Caveatron/Caveatron/RevB/documentation/RPLidar_modification_alternative_ver_02.pdf

## Lidar improvement

### Version: 2019.11.22 By Szymon Kostka

### Overview:

### Tests of the original lidar design

A. 4 mm thickness flat acrylic glass, about 20 mm distance between lidar and glass:

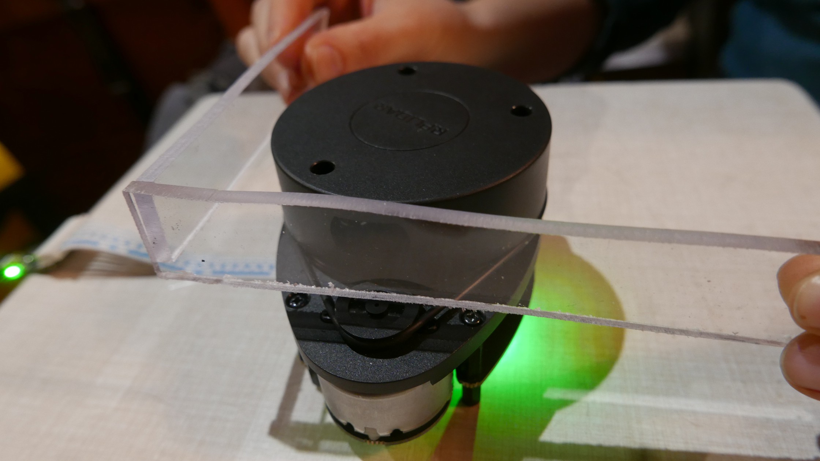
[picture p13: figure]

Test condions

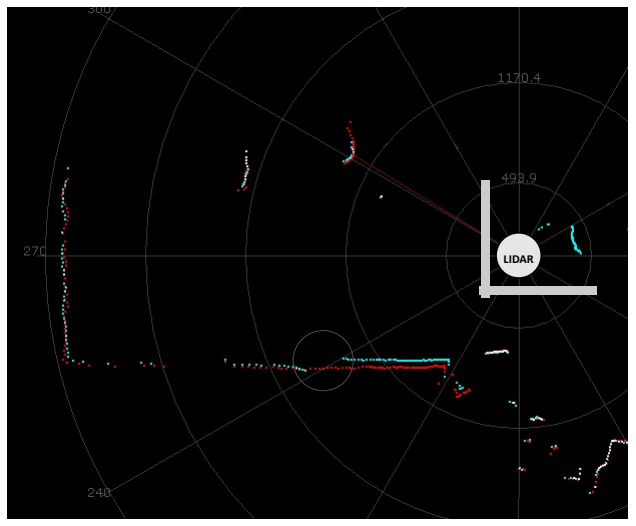
[picture p14: figure]
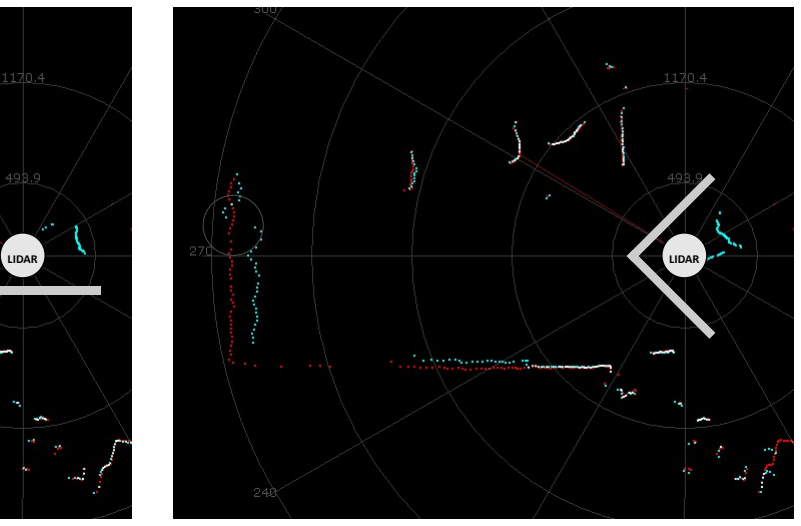
[picture p15: figure]
LIDAR

Scans. Blue dots: current state; red dots: reference image without distoron. Grey lines shows window posion.
A dark gray circle shows the locaon of the largest distorons.

Preparing to construct the housing for the lidar module, I decided to check what window shape would be the best. During the first tests, it turned out that the lidar opcal system is very sensive to distorons caused by the opcal properes of the shape and material of which the windows are made.
Tests have shown that windows made of straight secons of organic glass cause only local, but significant distorons. A window made of a pipe gives a very high distoron, the greater the farther away the scanned surface is. These distorons in the case of a pipe are also dependent on the wall thickness and distance from the opcal system. The thicker the wall and the closer to the opcs, the greater the distoron.

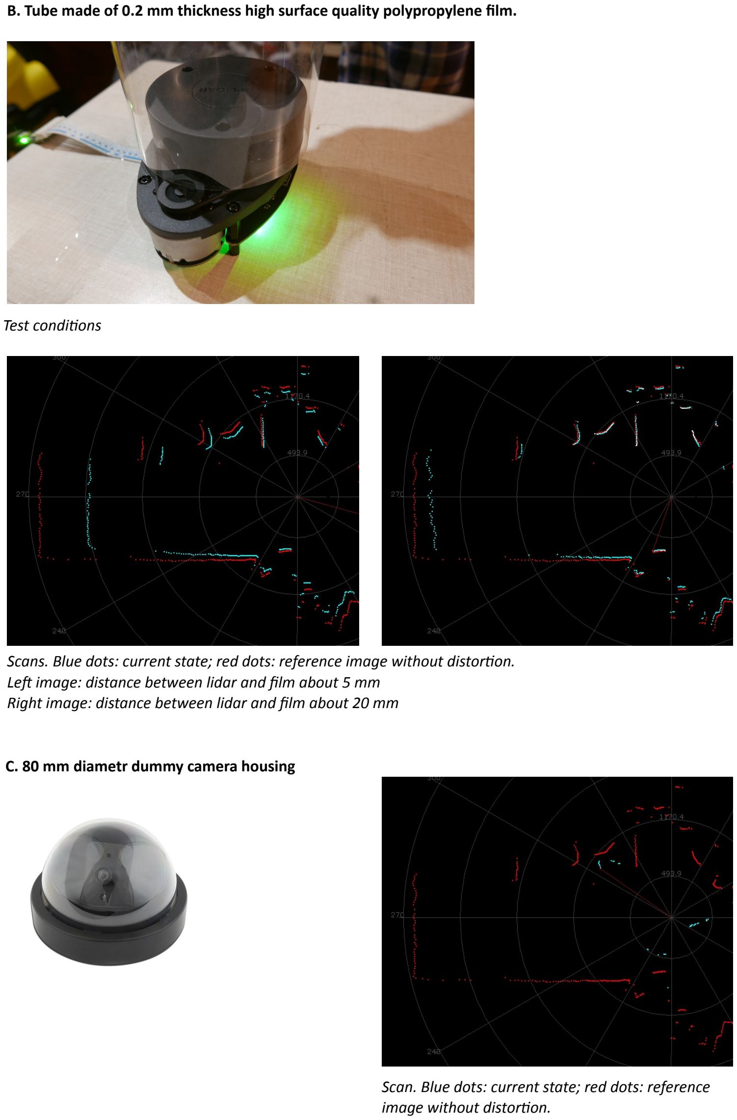
[picture p16: page 2]

B. Tube made of 0.2 mm thickness high surface quality polypropylene film.

Test condions

Scans. Blue dots: current state; red dots: reference image without distoron. Le image: distance between lidar and film about 5 mm
Right image: distance between lidar and film about 20 mm
C. 80 mm diametr dummy camera housing

Scan. Blue dots: current state; red dots: reference image without distoron.

### Conclusions:

### Modificaon of the lidar module:

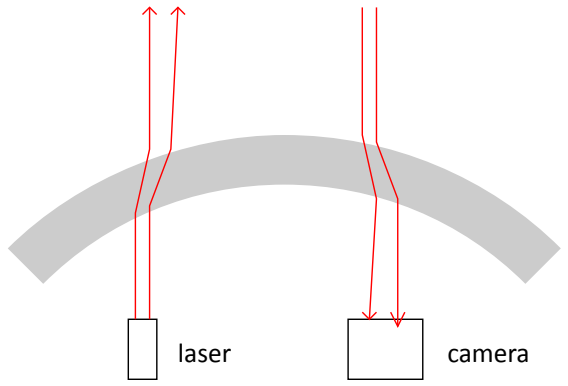
[picture p17: figure]
laser; camera

laser | camera

Simplified opcal model of different shapes of window Le: flat glass. Right: bended glass (acts as a lens).

laser
camera

Proposed modificaon of lidar, in which the laser and camera will work in the same axis.

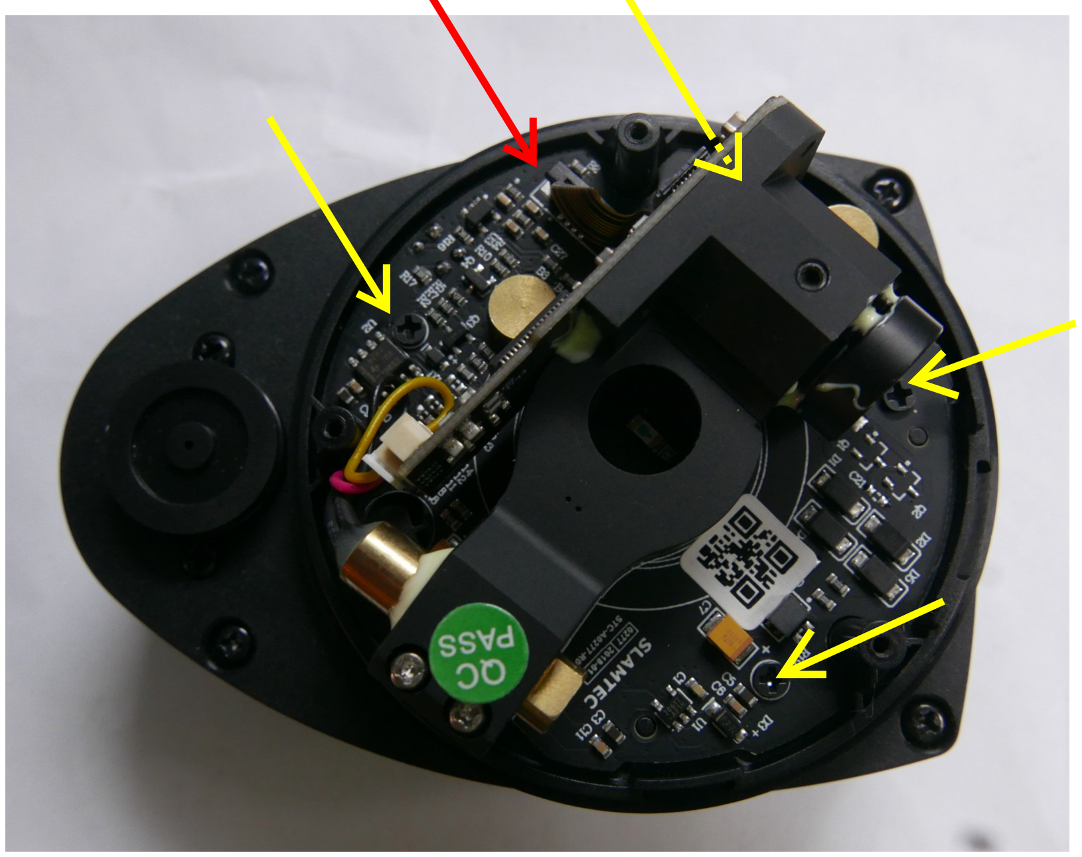
[picture p18: figure]

A.
- Remove drive belt
- Remove top cover.
- Disconnect the connecng tape from pcb pulling the brown lock out of the connector (red arrow)
- Unscrew 4 screws (yellow arrows):

The conducted experiments show that the shape of the lidar opcal path is distorted in various ways.
It mainly depends on the angle at which the lidar opcs are set to the window material. In flat glass,
the opcal path is mainly shied. In bent glass, the lens effect, which can almost completely disturb the operaon of lidar, has the greatest impact. Most of these distorons are affected by the fact that the laser
and camera work at different angles to the window material. Some soluon to the problem could be reworking the lidar so that the laser and camera work in one axis. Then the laser and camera shis should be the same. The conducted experiments and problem analysis show that a window from a tube (bent glass) will work worse than from straight glass secons.

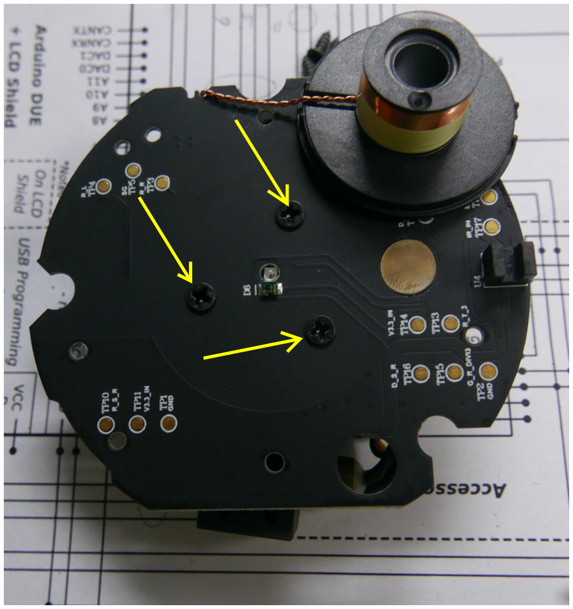
[picture p19: figure]

A.
- Remove drive belt
- Remove top cover.
- Disconnect the connecng tape from pcb pulling the brown lock out of the connector (red arrow)
- Unscrew 4 screws (yellow arrows):

C.
- Prepare a new fastening element for lidar opcs. Use an aluminum angle 2 mm thick.

47,50 mm

28,00 mm

You can draw holes with a transparent adhesive tape. You can also print an unfolded drawing, sck it on aluminum and punch the holes with a center punch

expanded drawing (1:1)

holes:
1.5 mm dia and thread M2
(metric!) for original screws
or 2 - 2.2 mm for screws with nut

holes:
Outside: 2 - 2.2 mm.

# Center: 3 mm ²²,00 mm

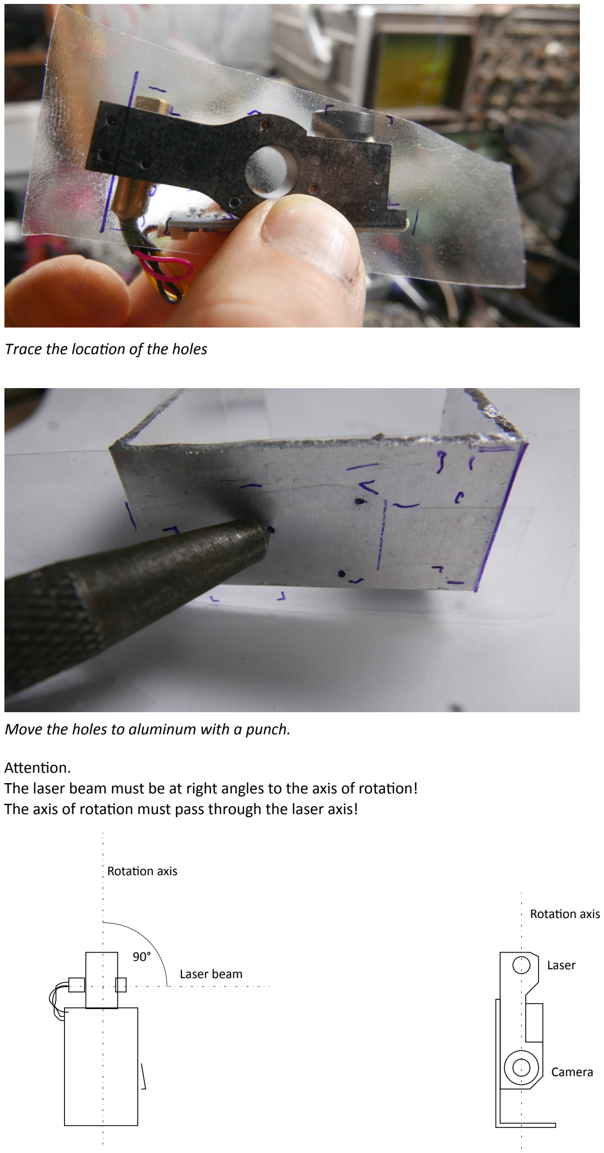
[picture p20: page 5]

Trace the locaon of the holes

Aenon.
The laser beam must be at right angles to the axis of rotaon! The axis of rotaon must pass through the laser axis!

90°

Rotaon axis

Laser beam

Rotaon axis

Laser

Camera

Move the holes to aluminum with a punch.

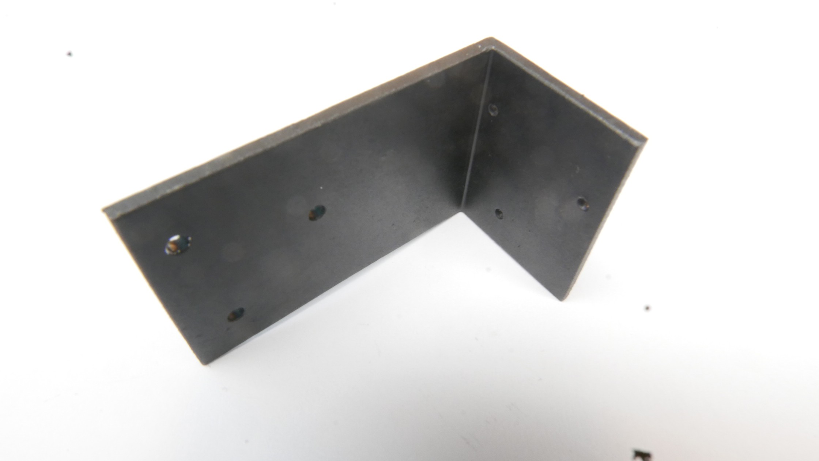
[picture p21: figure]

Ready element (without center hole)
D.
- Mount M3/30 screw to the center hole using one nut.
- Mount element to the PCB using original screws (don’t forget about the washers) using original screws or use M2/8 countersunk head screws with M2 nuts.
- Mount the opcs to the bracket using M2/5 screws.
- Connect the tape to the connector.
- Install the drive belt.

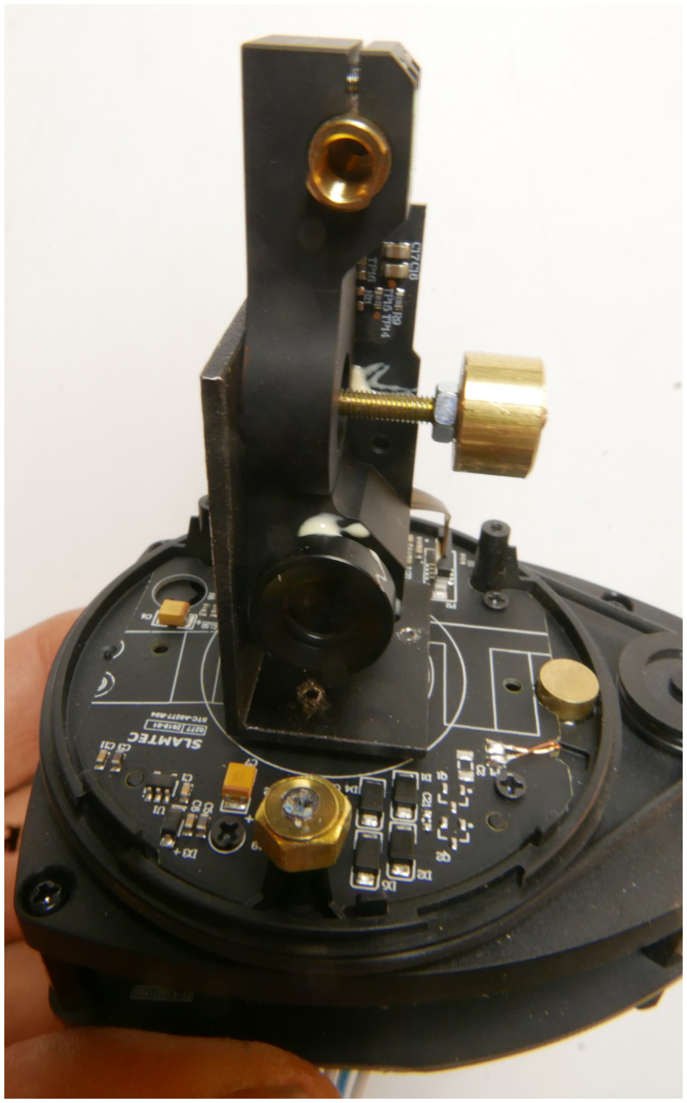
[picture p22: figure]

Ready module with balancing weights

E. Balancing:
Theorecally, the module is ready for work. But with a 5V motor voltage, its vibraon will be noceable and may make measurements difficult, especially on the long scanning distances. So it would be good to balance the rotang part. And this should be dynamic balancing!
I did it with two elements. In front of the camera lens, I put a M5 brass nut (can be steel) on the cover mounng post. The nut is fastened by an unnecessary cover screw through a 3 mm washer. The second
element is a lile more complicated. I used
a brass roller with a diameter of 12 mm,
which is 8 mm long and has a M3 thread inside. But you can try in a different way. For example, replace the M3/30 screw with the M4/40 screw and use several widened washers as ballast. You can also try fishing rod weights. They are small and in different shapes.
If you do not have access to special equipment, the balancing process should be carried out by trial and error. Check the vibraons aer each change to the sengs. It will help hang the lidar module on a string. The axis of rotaon must be vercal.

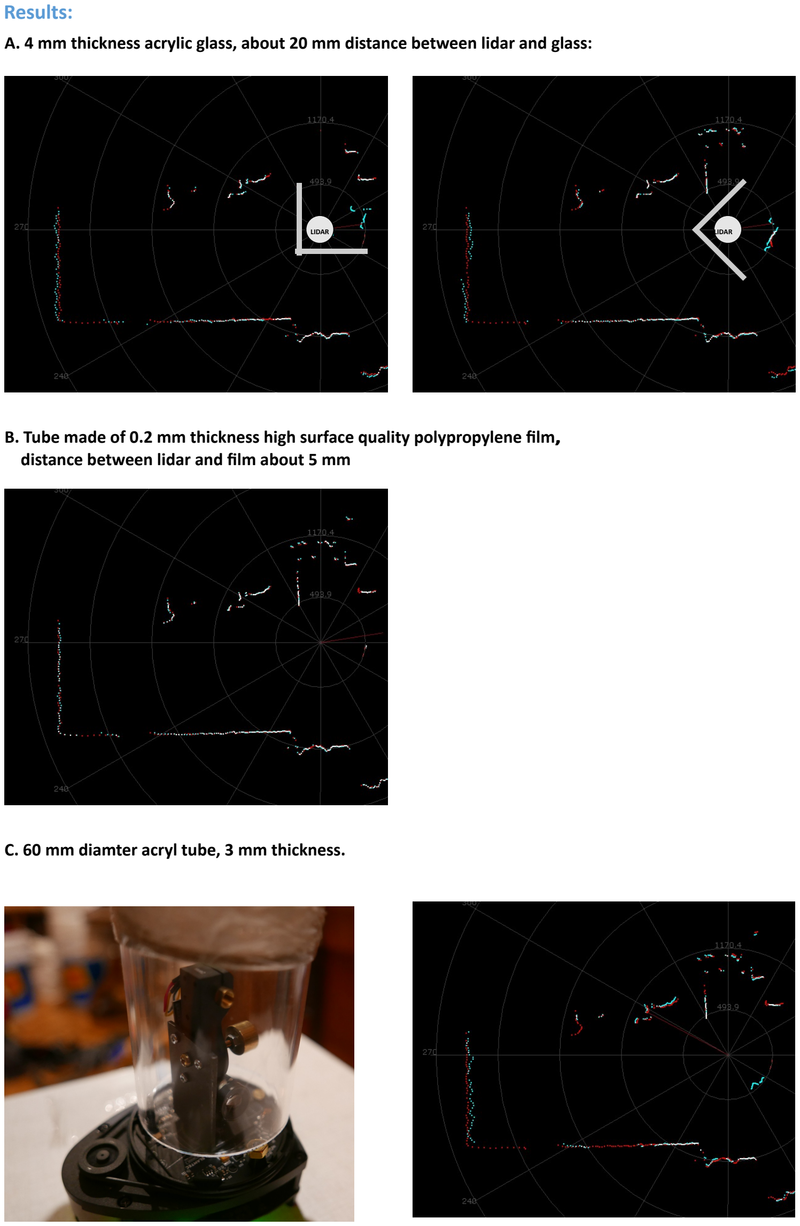
[picture p23: page 7]

### Results:

A. 4 mm thickness acrylic glass, about 20 mm distance between lidar and glass:
LIDAR | LIDAR
B. Tube made of 0.2 mm thickness high surface quality polypropylene film, distance between lidar and film about 5 mm

,

C. 60 mm diamter acryl tube, 3 mm thickness.

Table comparing the maximum measurement error between lidar without window and with window.

material | maximum error before update | maximum error aer update
4 mm thickness flat acrylic glass with 90° corners | 19% | 3%
Tube made of 0.2 mm PP film, 5 mm distance between film and lidar | 19% | < 1%
80 mm diametr dummy camera housing | no reading
60 mm diamter acryl tube, 3 mm thickness | | 4%
