Caveatron/Caveatron/RevC/mechanical/STEP files/LRF Bracket v3.step

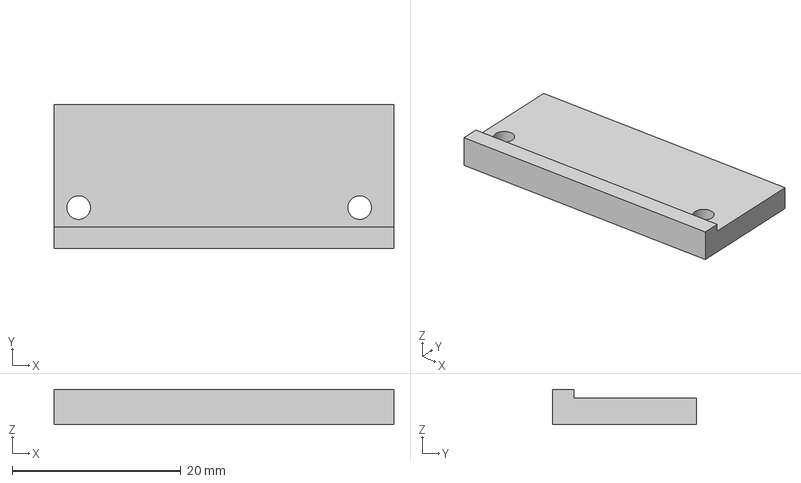
[picture p139: CAD file, 2022-12-10]
RevC/mechanical/STEP files/LRF Bracket v3.step
40.3 x 17.0 x 4.19 mm
