Caveatron/Caveatron/RevC/mechanical/STEP files/RPLIDAR S2 Rev C Base v7.step

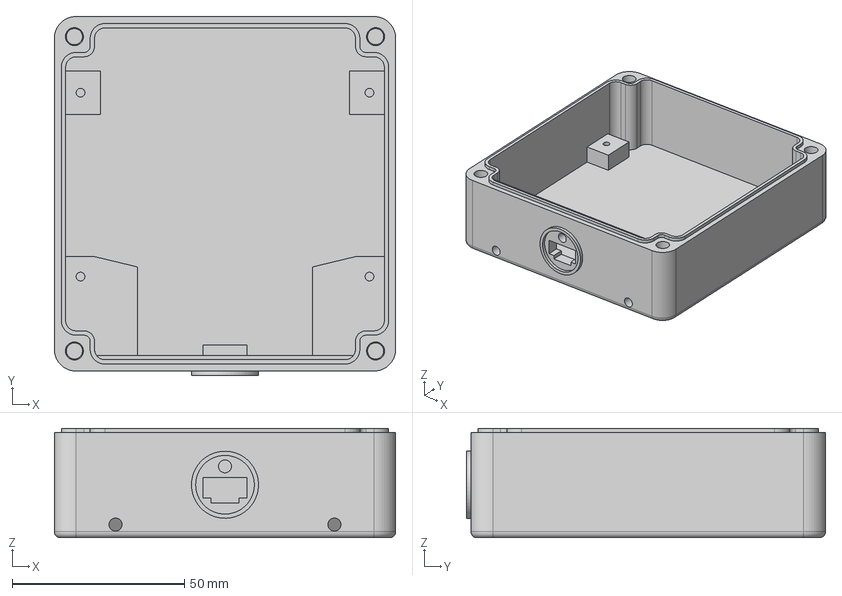
[picture p140: CAD file, 2022-12-10]
RevC/mechanical/STEP files/RPLIDAR S2 Rev C Base v7.step
99.1 x 104.1 x 31.8 mm
