Caveatron/Caveatron/RevC/mechanical/STEP files/MinIMU Bracket v1.step

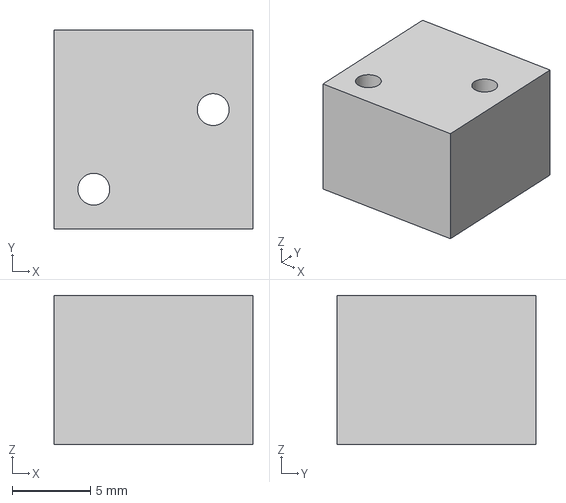
[picture p141: CAD file, 2022-12-10]
RevC/mechanical/STEP files/MinIMU Bracket v1.step
12.7 x 12.7 x 9.52 mm
