Caveatron/Caveatron/RevC/mechanical/STEP files/LRF Cradle v1.step

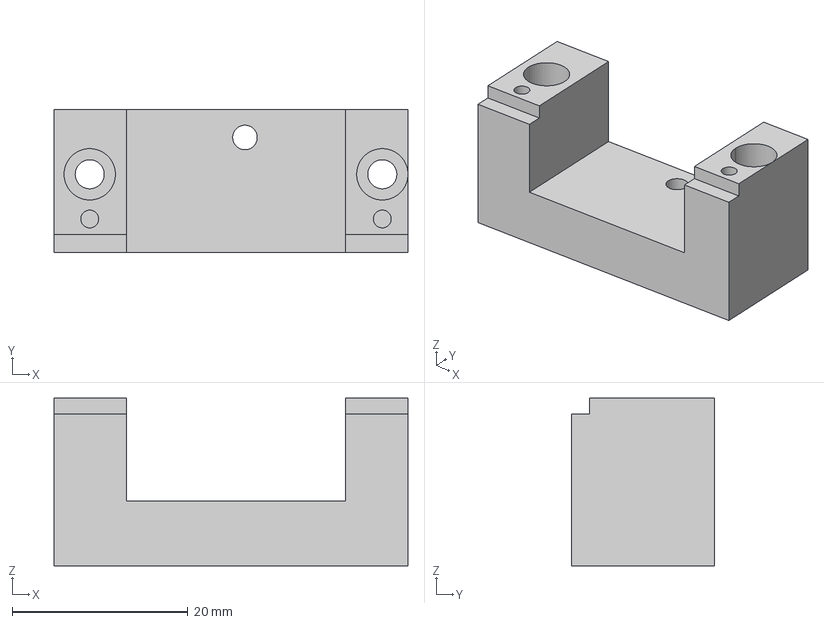
[picture p142: CAD file, 2022-12-10]
RevC/mechanical/STEP files/LRF Cradle v1.step
40.3 x 16.3 x 19.0 mm
