Caveatron/Caveatron/RevC/mechanical/STEP files/RPLIDAR S2 Rev C Lid - Dome v3.step

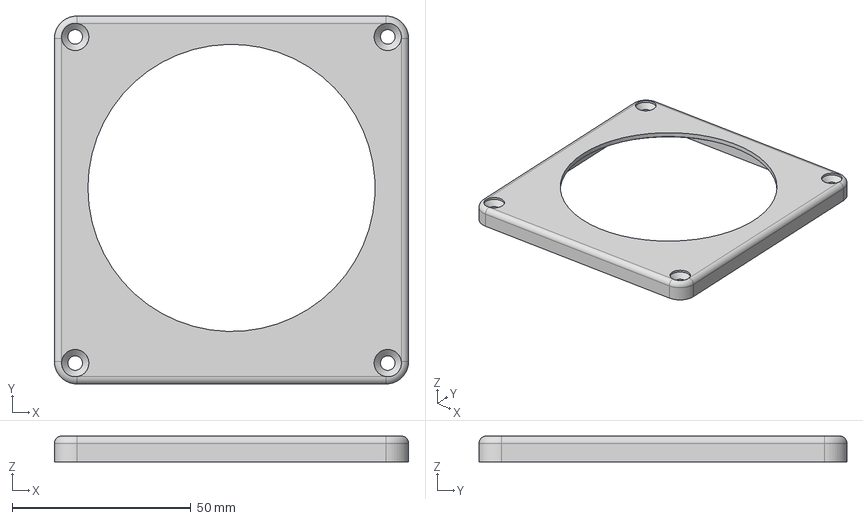
[picture p143: CAD file, 2022-12-10]
RevC/mechanical/STEP files/RPLIDAR S2 Rev C Lid - Dome v3.step
99.1 x 102.9 x 7.24 mm
