Caveatron/Caveatron/RevC/mechanical/STEP files/Buzzer Clamp v1.step

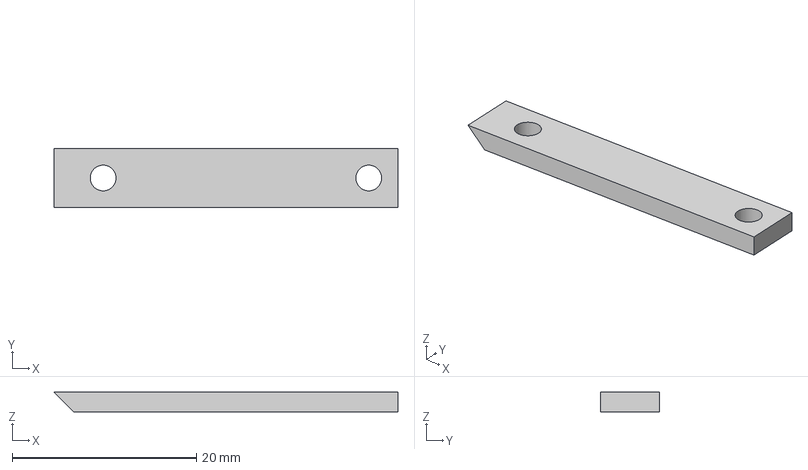
[picture p145: CAD file, 2022-12-10]
RevC/mechanical/STEP files/Buzzer Clamp v1.step
37.3 x 6.35 x 2.16 mm
