Caveatron/Caveatron/RevC/mechanical/STEP files/RM3100 Bracket v1.step

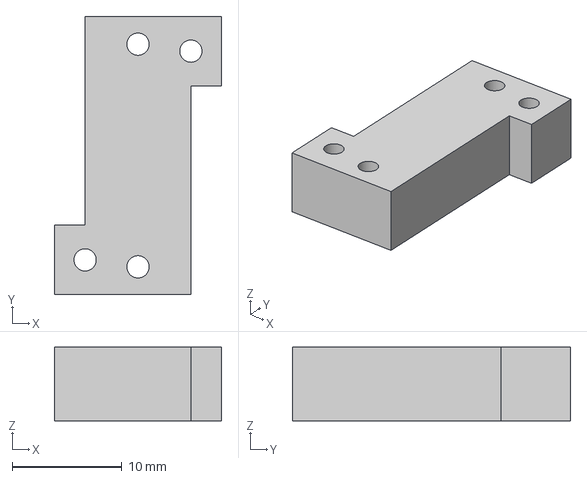
[picture p146: CAD file, 2022-12-10]
RevC/mechanical/STEP files/RM3100 Bracket v1.step
15.2 x 25.4 x 6.73 mm
