Caveatron/Caveatron/RevB/mechanical/LIDAR Windows Drawing v1.pdf

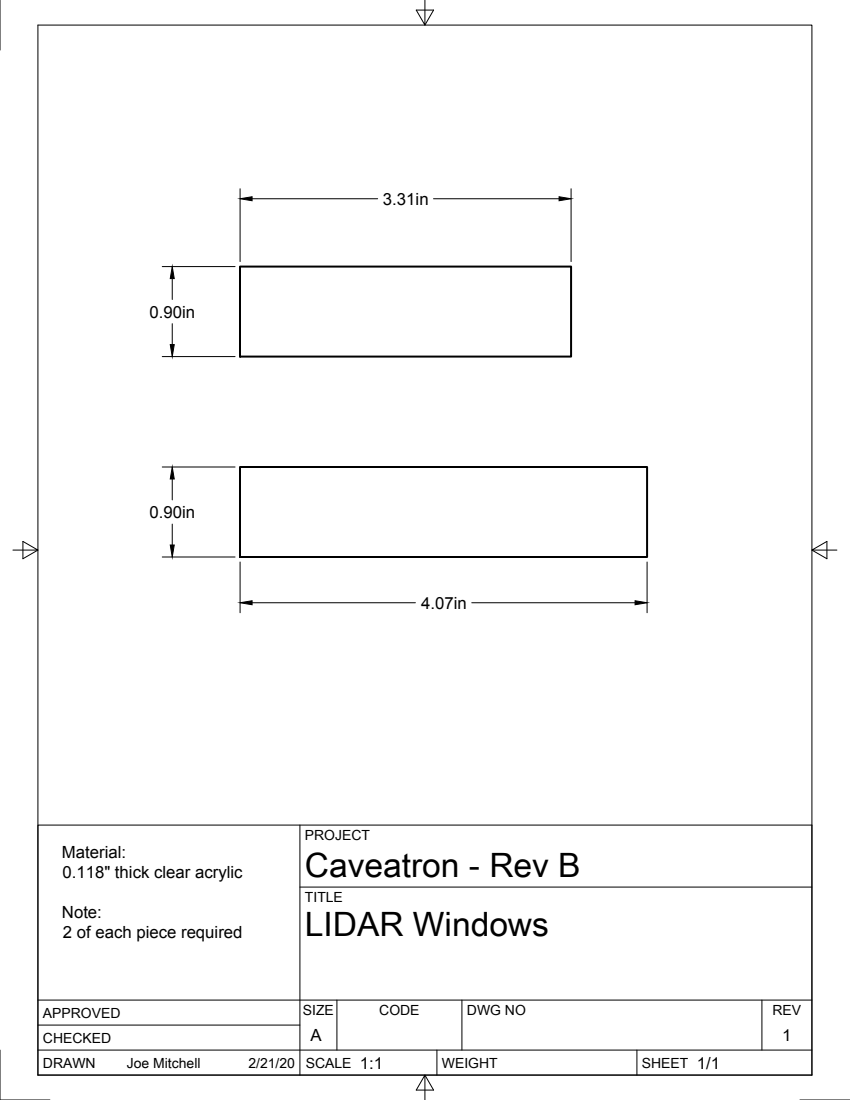
[picture p262: page 1]
SIZE; CODE; DWG NO; REV; Joe Mitchell; Caveatron - Rev B; LIDAR Windows

Material:
0.118" thick clear acrylic

Note:
2 of each piece required
