Caveatron/Caveatron/RevB/mechanical/LRF Window Drawing v1.pdf

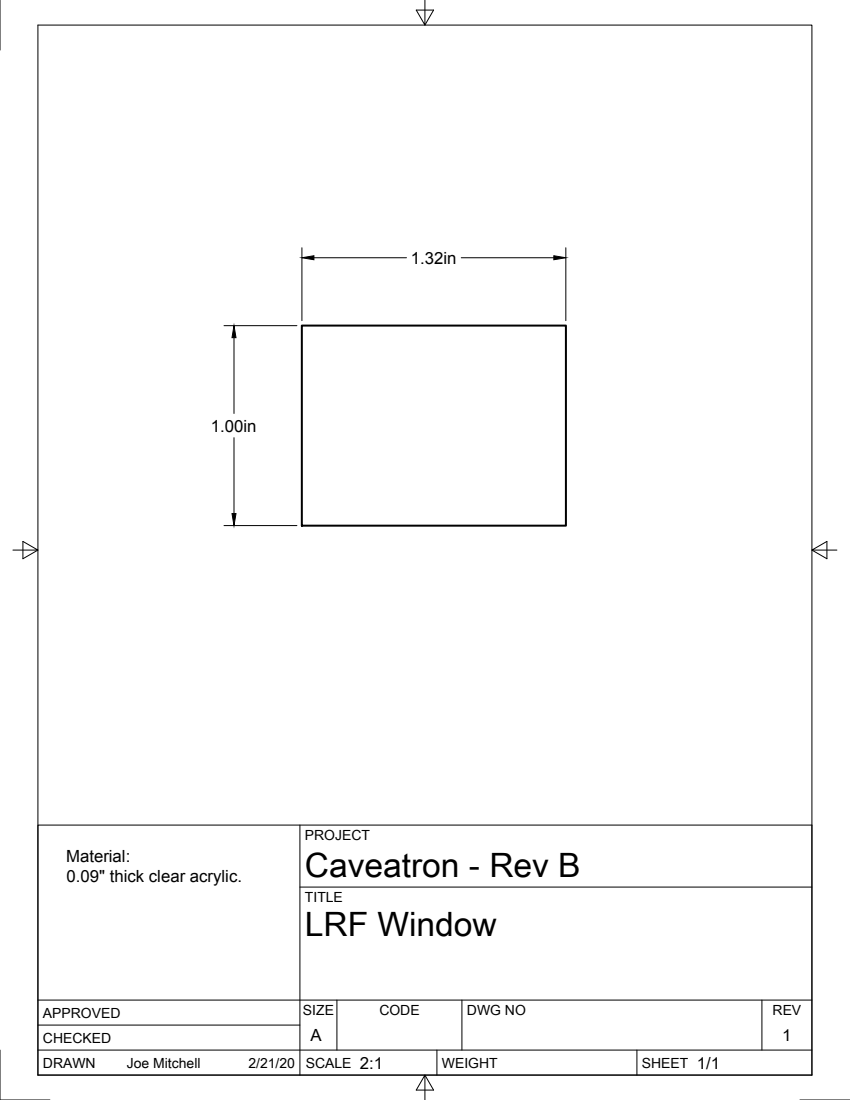
[picture p263: page 1]
SIZE; CODE; DWG NO; REV; Joe Mitchell; Caveatron - Rev B; LRF Window

Material:
0.09" thick clear acrylic.
