Caveatron/Caveatron/RevB/pcb/Caveatron RevB_1 PCB Schematic.pdf

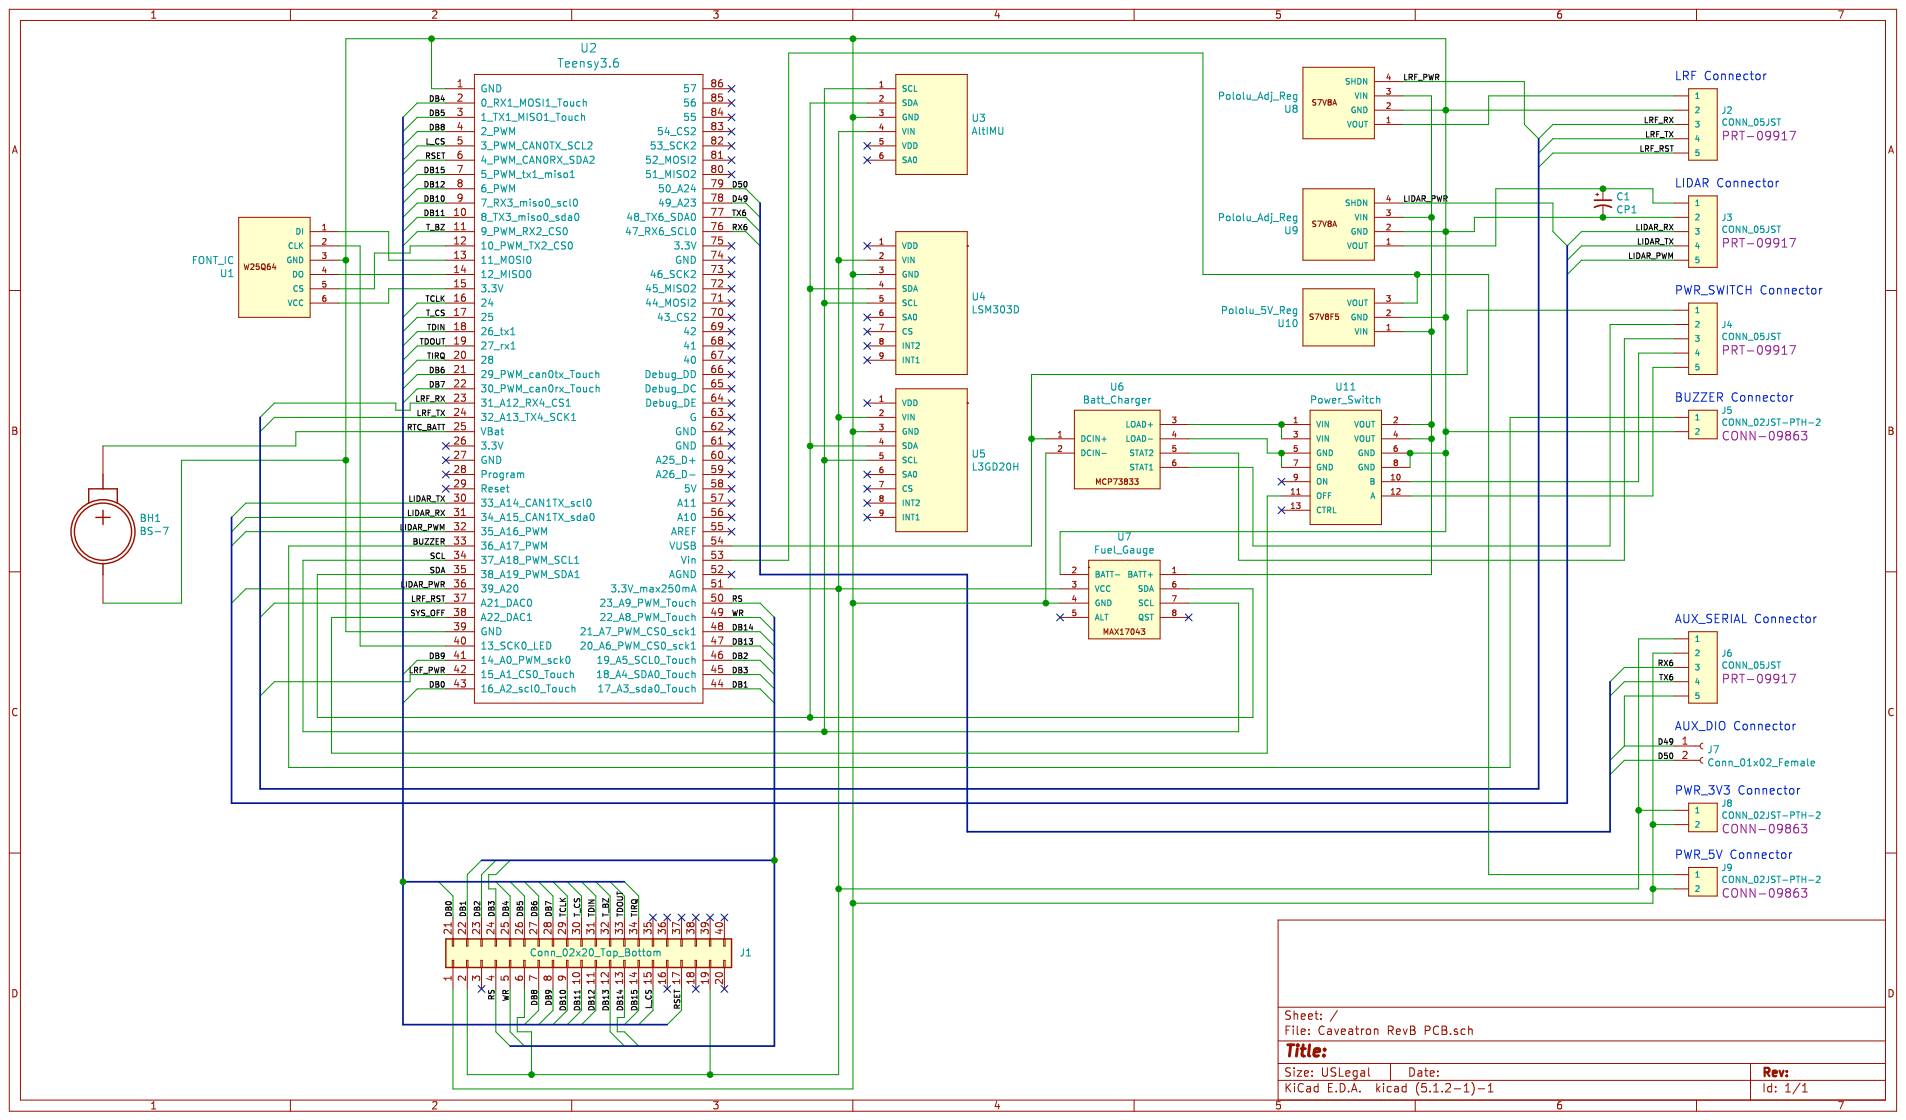
[picture p266: page 1]
