Caveatron/Caveatron/software/Caveatron_Parameter_Uploader_&_Downloader/Caveatron_Parameter_Uploader_v20/Calibration_Parameters.ino

//Caveatron Calibration Parameters
//Serial Number: TB000
//Date: 2019-09-29

extern char serialNumber[] = "TB000";

extern char hardwareCode[] = "B211112110-3";

extern char screenCal[3][11] = {"035E836BUL","00B24E8BUL","0013F1DFUL"};

//02-10-2017
extern float accCal[4][3] = {
  {-2.13659E-02,7.34896E-03,-2.78281E-02},
  {6.34247E-05,1.84463E-08,3.66437E-07},
  {1.38812E-08,6.26337E-05,-3.47865E-07},
  {-3.38732E-08,2.60433E-07,6.28441E-05}
};

//02-24-2017
extern float magAlignCal[8] = {-60,140,0,2.7,50,90,0,3.6};

extern float magCal[4][3] = {
  {2328.1503906,-1157.1542969,-373.3346863},
  {0.8116457,-0.0914898,0.0263052},
  {-0.0914897,0.9353983,0.0116162},
  {0.0263052,0.0116162,0.9962596}
};

//09-29-2019
extern float gyrCal[3] = {0,0,0};

extern float lidarCorners[4][2] = {
  {-1.0,-1.0},
  {124.1,125.5},
  {230.8,232.2},
  {322.3,323.6}
};

extern float lidarOrientCal[1] = {0};

extern float LRFRangeCal[1] = {0};

extern int8_t lidarWindowCorrectSettings[2] = {2,1};

extern int8_t lidarWindowCorrection[720] = {0,0,0,0,2,1,2,2,2,2,1,1,0,1,1,3,4,3,3,2,1,0,1,2,1,2,2,1,1,2,1,0,2,1,0,0,0,-1,-3,0,2,1,0,-1,-1,-2,-1,3,2,0,-2,-2,0,2,1,-1,-2,0,1,2,2,2,2,3,3,4,3,4,3,4,4,3,4,4,4,5,6,5,4,6,7,7,5,7,8,8,5,7,3,-6,-11,-13,-18,-16,77,75,67,60,55,54,53,49,54,55,53,54,49,54,60,58,56,55,56,59,56,55,55,55,57,-128,52,55,-128,-128,-128,-128,-128,-128,-128,62,60,60,58,58,55,55,57,62,66,66,63,60,59,58,55,54,54,58,60,60,60,60,62,66,70,38,1,-1,-3,1,1,1,-1,-4,-4,-4,-4,-3,-2,-2,-1,-1,-1,-3,-3,-1,-1,-3,-1,-1,-1,-2,-1,0,-1,-1,-2,-1,-2,-3,-1,-1,-2,-2,-2,-3,-3,-4,-4,-1,-3,-1,0,1,2,1,1,0,-1,-2,-3,-2,-1,0,-1,-1,0,-3,-9,-16,-22,-26,-28,-28,121,113,107,103,97,96,96,98,96,90,84,80,80,78,75,76,76,75,73,70,70,68,62,-128,-128,-128,-128,-128,-128,-128,-128,-128,-128,105,65,64,65,64,64,64,64,64,64,65,64,65,63,63,64,64,63,64,63,64,64,64,64,67,34,-3,-8,-15,-11,-3,-3,-2,-2,-2,-1,0,-3,-4,-2,-2,-2,-2,-3,-3,-1,-2,-3,-3,-2,-3,-3,-3,-2,-4,-1,-1,-2,-3,-3,-3,-2,-1,-2,-2,-1,-1,0,2,0,-1,0,1,0,0,0,1,0,-1,0,0,0,0,1,-1,-2,0,0,0,1,1,-1,1,0,0,1,1,0,0,2,0,0,0,0,-1,1,1,-1,-1,0,0,-1,0,-1,-1,0,1,-1,1,0,-1,-1,-1,-1,-1,-1,-1,-1,-2,-1,0,1,1,1,1,0,0,-1,1,0,-1,0,1,1,0,1,1,1,0,0,0,1,1,1,0,2,1,1,-2,-10,-15,-19,-24,-29,16,74,76,74,67,62,58,54,54,52,51,51,52,51,52,52,53,53,53,52,50,48,48,49,50,50,48,50,49,49,50,48,47,48,45,52,24,-128,-128,-128,-128,-128,-128,-128,-128,-58,-41,70,-128,110,50,47,46,45,46,46,44,46,47,47,44,43,45,47,47,45,46,47,47,46,45,46,46,45,45,45,45,48,50,45,38,-128,-2,-5,-8,-8,-5,0,2,2,2,0,0,0,0,1,2,3,2,1,1,1,1,1,1,1,2,2,1,2,2,2,1,3,2,3,2,1,3,4,3,2,2,0,0,0,0,0,0,0,0,0,0,1,0,0,1,-1,-1,1,2,1,0,0,-1,-1,-1,-1,1,1,0,0,-1,0,1,1,2,2,0,-1,-1,0,2,2,-1,-1,1,1,1,1,-6,-11,-16,-17,-20,-24,-30,-28,80,81,75,70,64,56,51,47,44,43,41,39,41,41,39,38,39,36,37,40,39,37,39,39,40,40,39,42,42,47,-128,-128,-128,-128,-128,-128,-128,-128,-128,-128,-128,-128,-128,-128,-128,-128,-128,50,48,47,45,46,50,48,43,47,49,49,46,47,49,47,46,45,47,47,46,48,49,48,48,49,50,53,52,52,51,50,50,52,50,20,-128,-12,-15,-12,-8,-4,-2,0,-2,-2,-2,0,1,0,0,1,1,1,1,1,1,2,1,1,1,1,1,1,1,2,1,1,1,0,0,0,-1,-1,1};
